arisberd/Infant-breath-mechanical-simulator/Photo and Video/electronics2.jpg

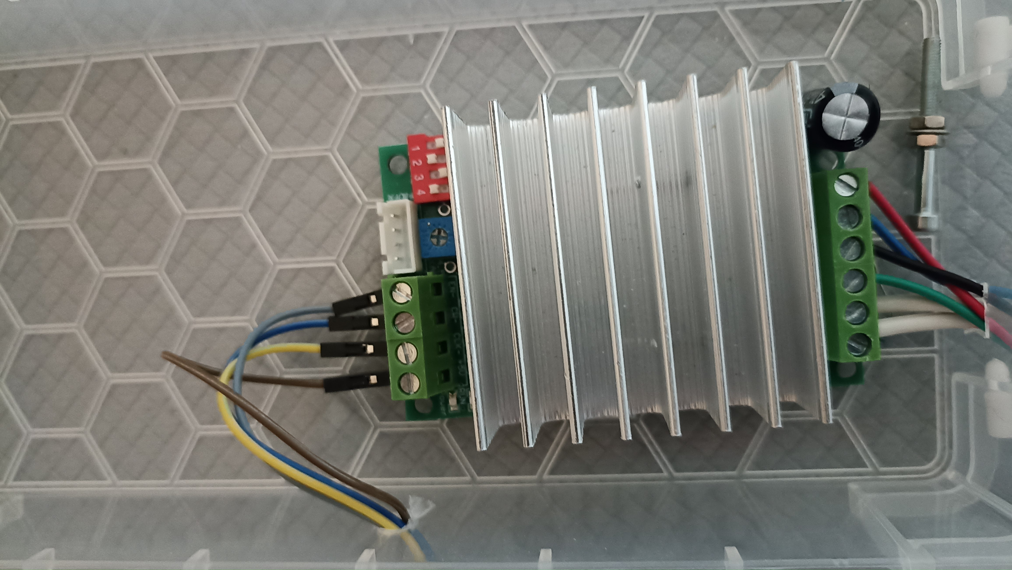
Photo and Video/electronics2.jpg
