arisberd/Infant-breath-mechanical-simulator/Photo and Video/electronics3.JPG

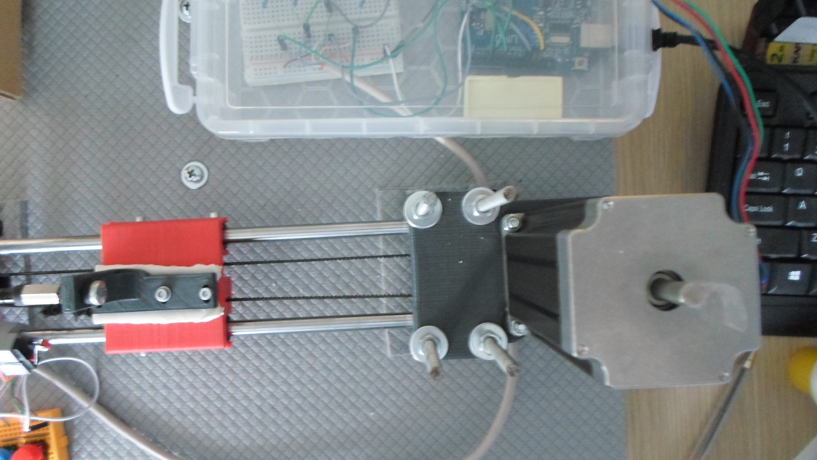
Photo and Video/electronics3.JPG
