arisberd/Infant-breath-mechanical-simulator/Photo and Video/motor_mount.jpg

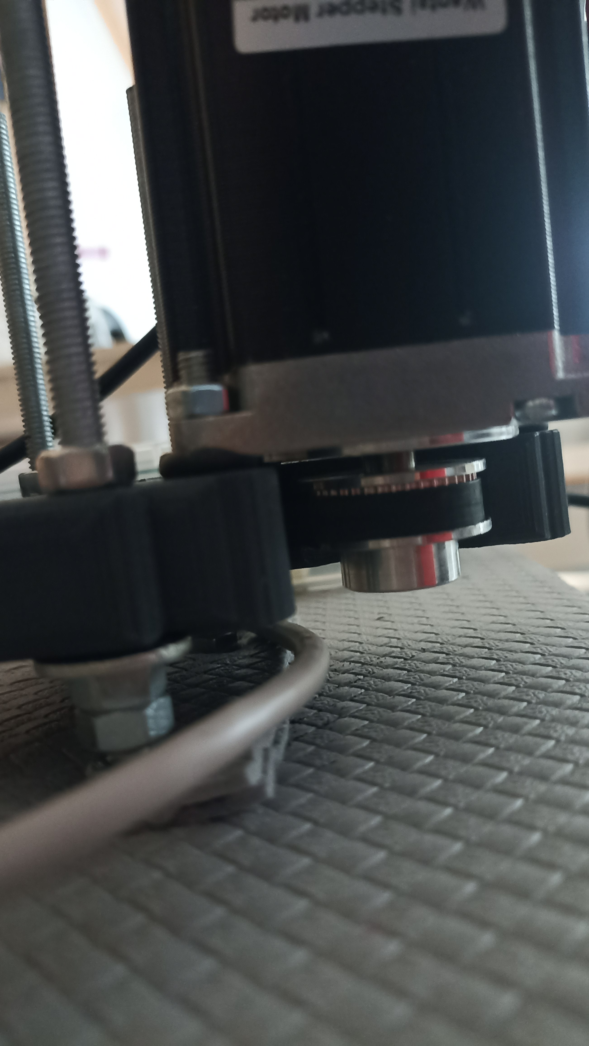
Photo and Video/motor_mount.jpg
