arisberd/Infant-breath-mechanical-simulator/Software/breath-sim/dataleo4.h

//Infant-breath-mechanical-simulator
//https://github.com/arisberd/Infant-breath-mechanical-simulator
//version 0.2
//GNU GPL v3

//Datasheet dataleo4.h

//Manual Input Data
// the data should be put as :
//VT , Ti, Te/Ti ratio,
//VT in ml, Ti in msec, Te/Ti in percentage
//ex
//10  , 500 , 140 ,
//15  , 700 , 100
//
const int PROGMEM manual_input[] = {



20	,	500	,	140	,
20	,	500	,	100	,
20	,	500	,	71	,
7.5	,	500	,	200	,
7.5	,	500	,	140	,
7.5	,	500	,	100	,
7.5	,	500	,	71	,
15	,	500	,	200	,
10	,	300	,	186	,
12.5	,	500	,	200	,
12.5	,	500	,	140	,
12.5	,	500	,	100	,
12.5	,	500	,	71	,
17.5	,	700	,	114	,
17.5	,	700	,	71	,
7.5	,	300	,	186	,
15	,	500	,	200	,
15	,	500	,	140	,
15	,	500	,	100	,
15	,	500	,	71	,
12.5	,	700	,	114	,
12.5	,	700	,	71	,
20	,	700	,	114	,
20	,	700	,	71	,
5	,	300	,	186	,
7.5	,	700	,	114	,
7.5	,	700	,	71	,
15	,	700	,	114	,
15	,	700	,	71	,
5	,	500	,	200	,
5	,	500	,	140	,
5	,	500	,	100	,
5	,	500	,	71	,
7.5	,	500	,	200	,
7.5	,	500	,	140	,
7.5	,	500	,	100	,
7.5	,	500	,	71	,
10	,	500	,	200	,
10	,	500	,	140	,
10	,	500	,	100	,
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


};
